molnarkares/i2c_hvsupply/firmware/tmr3.h

/*
    (c) 2016 Microchip Technology Inc. and its subsidiaries. You may use this
    software and any derivatives exclusively with Microchip products.

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
    IN NO EVENT WILL MICROCHIP BE LIABLE FOR ANY INDIRECT, SPECIAL, PUNITIVE,
    INCIDENTAL OR CONSEQUENTIAL LOSS, DAMAGE, COST OR EXPENSE OF ANY KIND
    WHATSOEVER RELATED TO THE SOFTWARE, HOWEVER CAUSED, EVEN IF MICROCHIP HAS
    BEEN ADVISED OF THE POSSIBILITY OR THE DAMAGES ARE FORESEEABLE. TO THE
    FULLEST EXTENT ALLOWED BY LAW, MICROCHIP'S TOTAL LIABILITY ON ALL CLAIMS IN
    ANY WAY RELATED TO THIS SOFTWARE WILL NOT EXCEED THE AMOUNT OF FEES, IF ANY,
    THAT YOU HAVE PAID DIRECTLY TO MICROCHIP FOR THIS SOFTWARE.

    MICROCHIP PROVIDES THIS SOFTWARE CONDITIONALLY UPON YOUR ACCEPTANCE OF THESE
    TERMS.
*/

#ifndef _TMR3_H
#define _TMR3_H

/**
  Section: Included Files
*/

#include <stdbool.h>
#include <stdint.h>

#ifdef __cplusplus  // Provide C++ Compatibility

    extern "C" {

#endif


/**
  Section: TMR3 APIs
*/

/**
  @Summary
    Initializes the TMR3

  @Description
    This routine initializes the TMR3.
    This routine must be called before any other TMR3 routine is called.
    This routine should only be called once during system initialization.

  @Preconditions
    None

  @Param
    None

  @Returns
    None

  @Comment
    

  @Example
    <code>
    main()
    {
        // Initialize TMR3 module
        TMR3_Initialize();

        // Do something else...
    }
    </code>
*/
void TMR3_Initialize(void);

/**
  @Summary
    This function starts the TMR3.

  @Description
    This function starts the TMR3 operation.
    This function must be called after the initialization of TMR3.

  @Preconditions
    Initialize  the TMR3 before calling this function.

  @Param
    None

  @Returns
    None

  @Example
    <code>
    // Initialize TMR3 module

    // Start TMR3
    TMR3_StartTimer();

    // Do something else...
    </code>
*/
void TMR3_StartTimer(void);

/**
  @Summary
    This function stops the TMR3.

  @Description
    This function stops the TMR3 operation.
    This function must be called after the start of TMR3.

  @Preconditions
    Initialize  the TMR3 before calling this function.

  @Param
    None

  @Returns
    None

  @Example
    <code>
    // Initialize TMR3 module

    // Start TMR3
    TMR3_StartTimer();

    // Do something else...

    // Stop TMR3;
    TMR3_StopTimer();
    </code>
*/
void TMR3_StopTimer(void);

/**
  @Summary
    Reads the TMR3 register.

  @Description
    This function reads the TMR3 register value and return it.

  @Preconditions
    Initialize  the TMR3 before calling this function.

  @Param
    None

  @Returns
    This function returns the current value of TMR3 register.

  @Example
    <code>
    // Initialize TMR3 module

    // Start TMR3
    TMR3_StartTimer();

    // Read the current value of TMR3
    if(0 == TMR3_ReadTimer())
    {
        // Do something else...

        // Reload the TMR value
        TMR3_Reload();
    }
    </code>
*/
uint16_t TMR3_ReadTimer(void);

/**
  @Summary
    Writes the TMR3 register.

  @Description
    This function writes the TMR3 register.
    This function must be called after the initialization of TMR3.

  @Preconditions
    Initialize  the TMR3 before calling this function.

  @Param
    timerVal - Value to write into TMR3 register.

  @Returns
    None

  @Example
    <code>
    #define PERIOD 0x80
    #define ZERO   0x00

    while(1)
    {
        // Read the TMR3 register
        if(ZERO == TMR3_ReadTimer())
        {
            // Do something else...

            // Write the TMR3 register
            TMR3_WriteTimer(PERIOD);
        }

        // Do something else...
    }
    </code>
*/
void TMR3_WriteTimer(uint16_t timerVal);

/**
  @Summary
    Reload the TMR3 register.

  @Description
    This function reloads the TMR3 register.
    This function must be called to write initial value into TMR3 register.

  @Preconditions
    Initialize  the TMR3 before calling this function.

  @Param
    None

  @Returns
    None

  @Example
    <code>
    while(1)
    {
        if(TMR3IF)
        {
            // Do something else...

            // clear the TMR3 interrupt flag
            TMR3IF = 0;

            // Reload the initial value of TMR3
            TMR3_Reload();
        }
    }
    </code>
*/
void TMR3_Reload(void);

/**
  @Summary
    Starts the single pulse acquisition in TMR3 gate operation.

  @Description
    This function starts the single pulse acquisition in TMR3 gate operation.
    This function must be used when the TMR3 gate is enabled.

  @Preconditions
    Initialize  the TMR3 with gate enable before calling this function.

  @Param
    None

  @Returns
    None

  @Example
    <code>
    uint16_t xVal;
    uint16_t yVal;

    // enable TMR3 singlepulse mode
    TMR3_StartSinglePulseAcquistion();

    // check TMR3 gate status
    if(TMR3_CheckGateValueStatus()== 0)
        xVal = TMR3_ReadTimer();

    // wait untill gate interrupt occured
    while(TMR3GIF == 0)
    {
    }

    yVal = TMR3_ReadTimer();
    </code>
*/
void TMR3_StartSinglePulseAcquisition(void);

/**
  @Summary
    Check the current state of Timer1 gate.

  @Description
    This function reads the TMR3 gate value and return it.
    This function must be used when the TMR3 gate is enabled.

  @Preconditions
    Initialize  the TMR3 with gate enable before calling this function.

  @Param
    None

  @Returns
    None

  @Example
    <code>
    uint16_t xVal;
    uint16_t yVal;

    // enable TMR3 singlepulse mode
    TMR3_StartSinglePulseAcquistion();

    // check TMR3 gate status
    if(TMR3_CheckGateValueStatus()== 0)
        xVal = TMR3_ReadTimer();

    // wait untill gate interrupt occured
    while(TMR3IF == 0)
    {
    }

    yVal = TMR3_ReadTimer();
    </code>
*/
uint8_t TMR3_CheckGateValueStatus(void);

/**
  @Summary
    Boolean routine to poll or to check for the overflow flag on the fly.

  @Description
    This function is called to check for the timer overflow flag.
    This function is usd in timer polling method.

  @Preconditions
    Initialize  the TMR3 module before calling this routine.

  @Param
    None

  @Returns
    true - timer overflow has occured.
    false - timer overflow has not occured.

  @Example
    <code>
    while(1)
    {
        // check the overflow flag
        if(TMR3_HasOverflowOccured())
        {
            // Do something else...

            // clear the TMR3 interrupt flag
            TMR3IF = 0;

            // Reload the TMR3 value
            TMR3_Reload();
        }
    }
    </code>
*/
bool TMR3_HasOverflowOccured(void);

#ifdef __cplusplus  // Provide C++ Compatibility

    }

#endif

#endif // _TMR3_H
/**
 End of File
*/
