molnarkares/i2c_hvsupply/firmware/pulsecount.h

/*
* Copyright (c) 2021-2022 Karoly Molnar <molnarkares@gmail.com>
*
* MIT license. See LICENSE for details.
 */
#ifndef PULSECOUNT_H
#define	PULSECOUNT_H

#ifdef	__cplusplus
extern "C" {
#endif


uint24_t getPulseCount(void);


#ifdef	__cplusplus
}
#endif

#endif	/* PULSECOUNT_H */
