molnarkares/i2c_hvsupply/firmware/reset.h

/*
* Copyright (c) 2021-2022 Karoly Molnar <molnarkares@gmail.com>
*
* MIT license. See LICENSE for details.
 */
#ifndef RESET_H
#define	RESET_H

#ifdef	__cplusplus
extern "C" {
#endif

void swReset(void);


#ifdef	__cplusplus
}
#endif

#endif	/* RESET_H */
